nicolascaporaso/cuantico/src/llamada.py

"""Modo llamada: Cuántico conversa con un humano externo por altavoz/micro físicos.

Flujo de uso:
    1. nico: "Cuántico, voy a llamar a La Mafia para reservar mesa 2 personas mañana 21h".
    2. Cuántico llama la tool `iniciar_modo_llamada(objetivo)`, que setea un flag.
    3. Cuántico responde en personaje ("coge el móvil, yo me encargo") y termina el TTS.
    4. El main loop detecta el flag y llama a `llamada.ejecutar(objetivo, _hablar)`.
    5. nico pone el móvil en altavoz al lado del cilindro y marca al restaurante.
    6. Cuántico, con prompt distinto (profesional), conduce la conversación.
    7. Termina por `[FIN_LLAMADA]` en la respuesta, timeout global, o silencio prolongado.

Decisiones:
- Mientras Cuántico habla, el micro NO escucha (usamos `_hablar` que ya bloquea).
- Un `sleep(0.3)` tras hablar evita que el micro capte el eco del propio altavoz.
- El marcador `[FIN_LLAMADA]` lo genera el modelo al despedirse; se elimina del TTS.
"""
import time

import config
import micro
import luces
import cuantico_profiles as profile
from openrouter_client import OpenRouterChatSession


FIN_MARKER = "[FIN_LLAMADA]"
TIMEOUT_TOTAL_S = 180
TIMEOUT_SILENCIO_MS = 10000
SILENCIO_CUELGUE_MS = 45000

def _filtrar_fin(chunks, estado):
    """Reemite chunks de texto quitando el marcador [FIN_LLAMADA].
    Mantiene un buffer de cola para que el marcador partido entre chunks se detecte igual.
    `estado["terminar"]` queda a True si se vio el marcador; `estado["texto"]` acumula todo para log."""
    buffer = ""
    hold = len(FIN_MARKER) - 1  # chars retenidos por si el marcador está partido al final
    for chunk in chunks:
        t = chunk if isinstance(chunk, str) else (getattr(chunk, "text", None) or "")
        if not t:
            continue
        estado["texto"] += t
        buffer += t
        if FIN_MARKER in buffer:
            i = buffer.index(FIN_MARKER)
            pre = buffer[:i]
            if pre:
                yield pre
            estado["terminar"] = True
            return
        if len(buffer) > hold:
            emit = buffer[:-hold]
            buffer = buffer[-hold:]
            if emit:
                yield emit
    # Fin de stream: vuelca la cola
    if FIN_MARKER in buffer:
        i = buffer.index(FIN_MARKER)
        if buffer[:i]:
            yield buffer[:i]
        estado["terminar"] = True
    elif buffer:
        yield buffer


def ejecutar(objetivo: str, hablar_fn, hablar_stream_fn=None):
    """Corre el loop de llamada. Bloquea hasta que termine.

    `hablar_fn(texto, emocion)` se usa para frases cortas de sistema (errores).
    `hablar_stream_fn(generador, emocion)` se usa para las respuestas del modelo en streaming."""
    print(f"📞 === MODO LLAMADA ACTIVADO ===")
    print(f"📞 Objetivo: {objetivo}")

    system = profile.render_call_prompt(objetivo, FIN_MARKER)
    chat = OpenRouterChatSession(
        system,
        [],
        model=config.OPENROUTER_CALL_MODEL,
        enable_web_search=True,
    )

    # Cuántico NO saluda primero. Espera a que el camarero descuelgue y hable.
    # Tampoco interrumpe con "¿sigues ahí?": escucha en silencio hasta que el humano hable
    # o hasta que acumule SILENCIO_CUELGUE_MS de silencio seguido (cuelgue real).
    inicio = time.time()
    silencio_acumulado_ms = 0

    while time.time() - inicio < TIMEOUT_TOTAL_S:
        luces.cambiar_estado("escuchando")
        print("📞 Escuchando al humano…")
        texto_humano = micro.escuchar_seguimiento(timeout_ms=TIMEOUT_SILENCIO_MS)

        if not texto_humano:
            silencio_acumulado_ms += TIMEOUT_SILENCIO_MS
            if silencio_acumulado_ms >= SILENCIO_CUELGUE_MS:
                print(f"📞 {silencio_acumulado_ms}ms de silencio — cuelgue detectado.")
                break
            # Sigue escuchando sin decir nada. El camarero puede estar pensando, tecleando, etc.
            continue

        silencio_acumulado_ms = 0
        print(f"📞 Interlocutor: {texto_humano}")

        # Si nico dice algo como "cuántico corta" / "gracias cuántico", salimos sin más
        low = texto_humano.lower()
        if any(f in low for f in ("cuántico corta", "cuantico corta", "cuántico cuelga", "cuantico cuelga")):
            print("📞 nico ha pedido colgar.")
            break

        luces.cambiar_estado("pensando")
        print("📞 ↗ Enviando a OpenRouter (stream)…")
        try:
            stream = chat.send_message_stream(texto_humano)
        except Exception as e:
            print(f"⚠️ Modo llamada: fallo OpenRouter ({e}). Continuamos.")
            hablar_fn("Perdón, ¿puede repetirlo?", "sarcasmo")
            continue

        estado = {"terminar": False, "texto": ""}
        generador = _filtrar_fin(stream, estado)

        try:
            if hablar_stream_fn is not None:
                hablar_stream_fn(generador, "sarcasmo")
            else:
                # Fallback: agotamos el stream y hablamos del tirón.
                texto_resp = "".join(generador).strip()
                if texto_resp:
                    hablar_fn(texto_resp, "sarcasmo")
        except Exception as e:
            print(f"⚠️ Modo llamada: fallo reproduciendo stream ({e}).")
            hablar_fn("Perdón, un momento.", "sarcasmo")
            continue

        print(f"📞 Cuántico: {estado['texto'].replace(FIN_MARKER, '').strip()}")
        if estado["terminar"]:
            break

    _fin()


def _fin():
    print("📞 === MODO LLAMADA: FIN ===")
    luces.cambiar_estado("esperando")
